rabidaudio/synthesizer/amp/Annotation 2020-08-30 154602.png

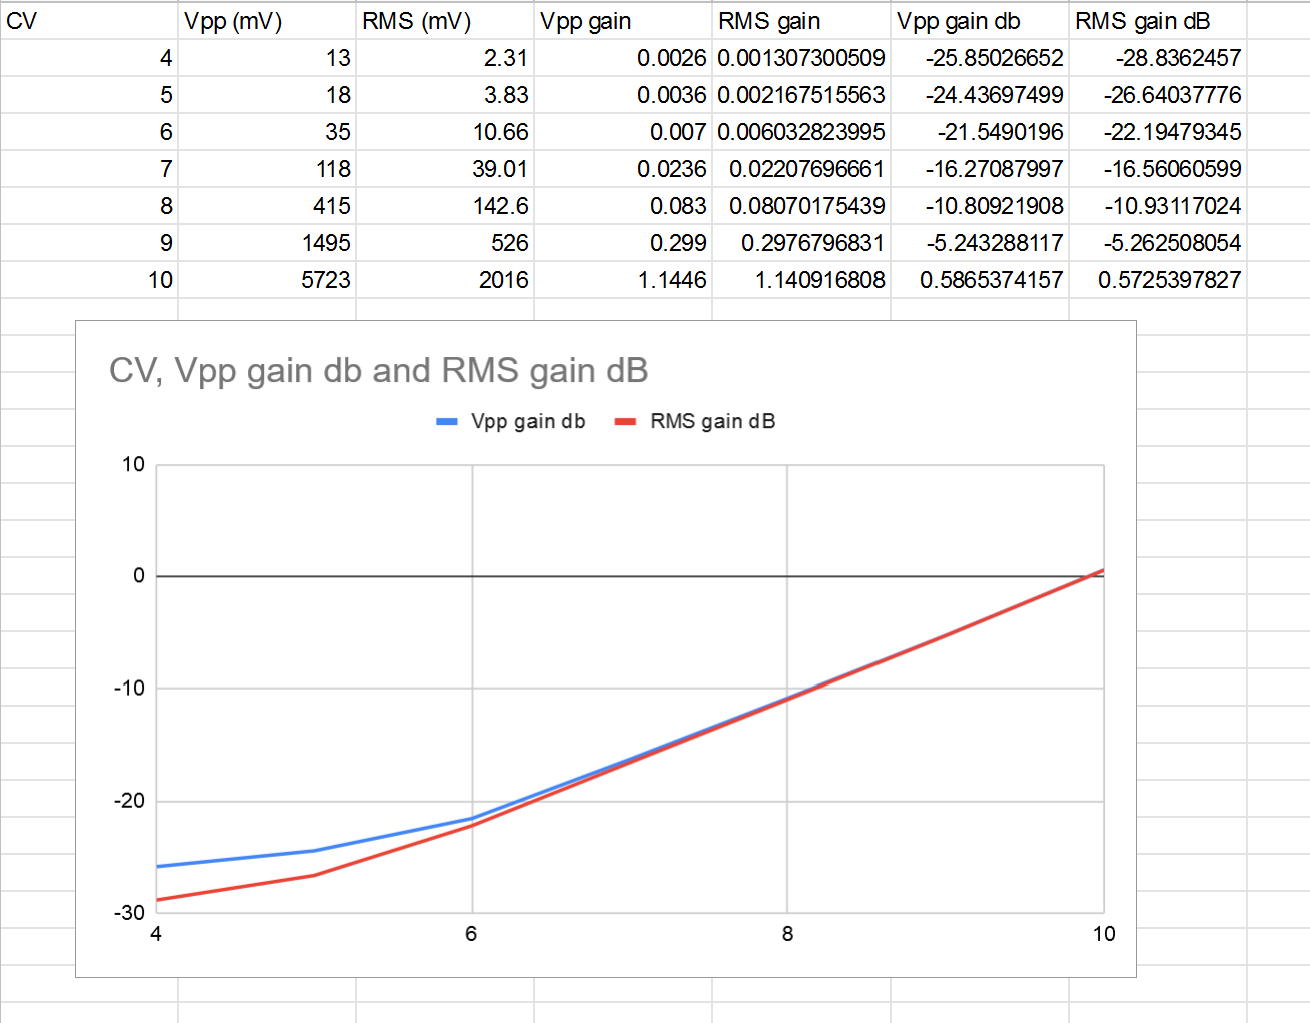
amp/Annotation 2020-08-30 154602.png
