rabidaudio/synthesizer/clock/panel/assets/103_grunge_splatter/Blood-Splatter-006.png

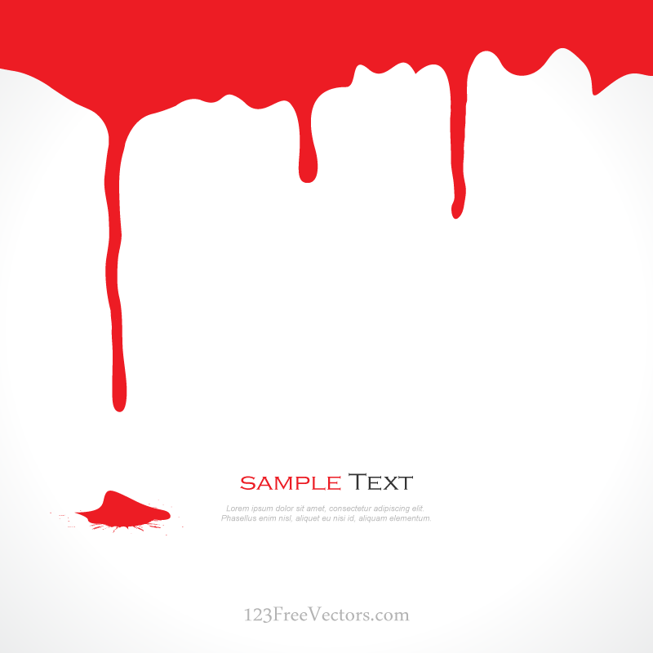
clock/panel/assets/103_grunge_splatter/Blood-Splatter-006.png
