rabidaudio/synthesizer/clock/panel/assets/nosferatu-cine-elhype.jpg

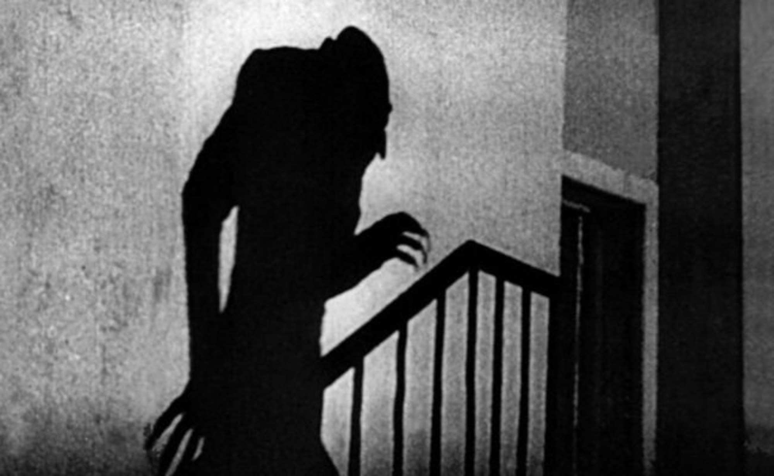
clock/panel/assets/nosferatu-cine-elhype.jpg
