rabidaudio/synthesizer/clock/panel/assets/nosferatu-outline.png

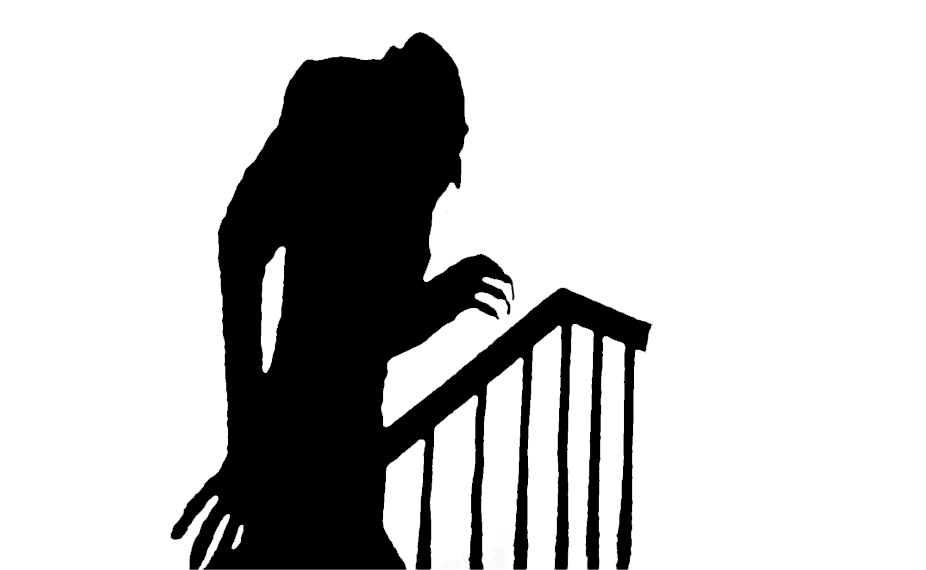
clock/panel/assets/nosferatu-outline.png
