rabidaudio/synthesizer/clock/panel/assets/Schreck.jpg

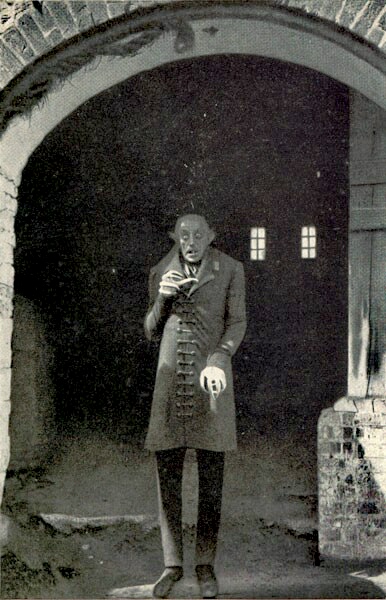
clock/panel/assets/Schreck.jpg
