rabidaudio/synthesizer/vco/vco2.png

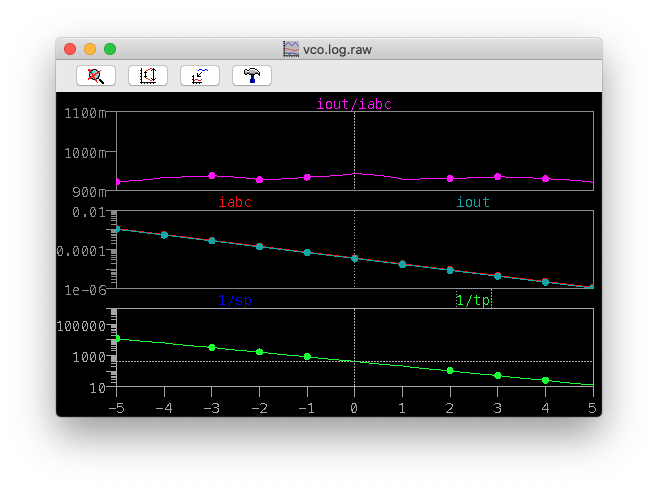
vco/vco2.png
