rabidaudio/synthesizer/vco/waveshaper-plot.png

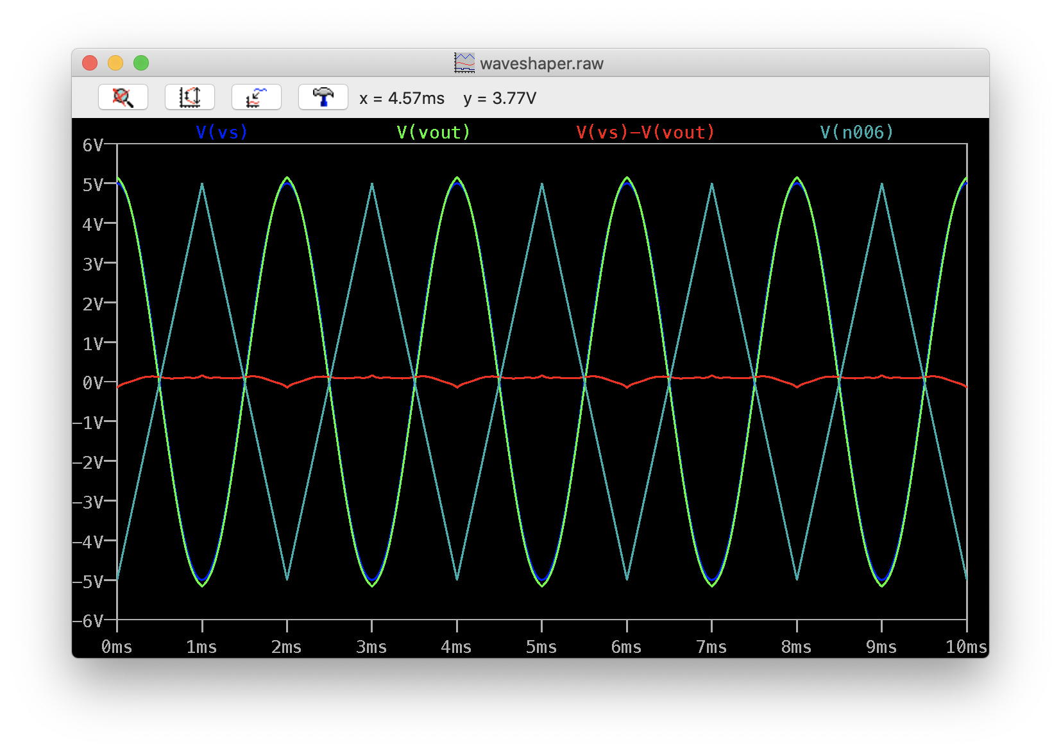
vco/waveshaper-plot.png
