rabidaudio/synthesizer/adsr/Draft1.asc

C1: cap; 4.7µ
I1: current; PULSE(2u -2u 0 0 0 1 2)
R1: res; {RC}
V1: voltage; PULSE(5 -5 0 0 0 1 2)
Named nets: 0, vout
.tran 10 UIC
.step param RC 50k 250k 25K
