rabidaudio/synthesizer/vco/gilbertcell-notworking.asc

Q1: npn
Q2: npn
Q3: npn
Q4: npn
Q5: npn
Q6: npn
R1: res; 3k
R2: res; 6k
R3: res; 6k
R4: res; 6k
U1: tl07x
V1: voltage; 12
V2: voltage; 12
V3: voltage; PULSE(-.1 .1 0 10m 10m 0 20m)
V4: voltage; PULSE(-.1 .1 0 0 0 5m 10m)
Named nets: 0, v+, v-, vo+, vo-, v1, v2
.tran 100m
