rabidaudio/synthesizer/vco/suboctave.asc

A1: dflop
A2: dflop
R1: res; 68K
R2: res; 47K
R3: res; 40k
R4: res; 10k
R5: res; 100k
R6: res; 100k
U1: tl07x
U2: tl07x
U3: ADG1633
U4: tl07x
V1: voltage; 12
V2: voltage; 12
V3: voltage; PULSE(-5 5 0.74m 0 0 0.5m 1m)
V4: voltage; SINE(0 5 1k)
V5: voltage; PULSE(5 0 .5m 0 0 1m 2m)
Named nets: 0, v+, v-, vsin, vsq, ~vsin, vout
.tran 10m
