rabidaudio/synthesizer/vco/vco.asc

C1: cap; 4.7n
Q1: pnp
Q2: pnp
R1: res; 4.7K
R2: res; 1k8
R3: res; 326K
R4: res; 15K
R5: res; 10K
R6: res; 100K
R7: res; 500
R8: res; 500
R9: res; 10K
R10: res; 10K
R11: res; 240K
U1: LM13700
U2: tl07x
U3: tl07x
U4: tl07x
V1: voltage; 12
V2: voltage; 12
V4: voltage; {CV}
Named nets: 0, V-, V+, v+, v-, VCV, sq, tri
.lib lm13700.sub
.lib opamp.sub
## CV-freq analysis ##
#.step param CV 0 10 1
# .tran 0 220m UIC
# .tran 0 8 UIC
# .meas tp TRIG V(tri)=0 RISE=2 TARG V(tri)=0 RISE=3
# .meas sp TRIG V(sq)=0 RISE=2 TARG V(sq)=0 RISE=3
# .meas iabc param -1*Ic(q2)
# .meas TRAN iout param abs(I(C1)) WHEN V(tri)=0 RISE=2
## R6 Analysis CV=5 ##
#.step param RA 98k 102K 100
#.meas tp TRIG V(tri)=0 RISE=2 TARG V(tri)=0 RISE=3
#.param CV 5
#.tran 0 500m UIC
## R3 Analysis CV=0 ##
#.step param RREF 320K 330K 100
#.meas tp TRIG V(tri)=0 RISE=2 TARG V(tri)=0 RISE=3
.tran 10m UIC
## High-freq accuracy CV=-5 ##
# .tran 200u UIC
## DC CV analysis ##
# .dc V4 0 10 1
