rabidaudio/synthesizer/utils/connect-logic.asc

Q1: npn
Q2: npn
R1: res; 100K
R2: res; 100K
R3: res; 100K
R4: res; 100K
V1: voltage; 5
Named nets: 0
.op
