rabidaudio/synthesizer/vco/cv-protection.asc

D1: diode
R1: res; 10k
R2: res; 47k
R3: res; 33k
R4: res; 18k
R5: res; 13k
U1: LT1001
V1: voltage; 12
V2: voltage; 12
V3: voltage; PULSE(-12 12 0 1m 1m 0 2m)
Named nets: 0, V+, V-
.tran 100u 10m
