rabidaudio/synthesizer/clock/src/PauseState.h

#pragma once

#include <Arduino.h>

// Keep track of if output is paused or not
class PauseState
{
private:
    bool _paused = false;
    bool _held = false;
    bool _pressed = false;

public:
    void setState(bool buttonsPressed)
    {
        if (!_held && buttonsPressed)
        {
            _paused = !_paused;
        }
        _held = buttonsPressed;
    }

    // debounce either button to issue tap
    bool isTap(bool buttonPressed)
    {
        if (_pressed == buttonPressed)
        {
            return false;
        }
        _pressed = buttonPressed;
        return buttonPressed;
    }

    bool isPaused()
    {
        return _paused;
    }

    void reset()
    {
        _paused = false;
    }
};
