rabidaudio/synthesizer/clock/src/Timer.h

#pragma once

#include <Arduino.h>
#include <util/atomic.h>
#include "Settings.h"

#define MIN_CLOCK (uint16_t)15
#define MAX_CLOCK (uint16_t)1600
#define MIN_BPM MIN_CLOCK
#define MAX_BPM (MAX_CLOCK / 4)

// Lookup table for OCR1A register values for BPMs from 15 to 1600.
// This is to avoid floating point math.
// 120 BPM = 2 Hz = (16000000/((7811+1)*1024))
// Calculations:
// https://docs.google.com/spreadsheets/d/1pTg9IQDEw8LUGN85Lwp80kAzATN1I9yxx0m5xDrEWBg/edit#gid=0
const PROGMEM uint16_t CLOCK_LOOKUP[] = {
    62500, 58593, 55147, 52083, 49342, 46875, 44642, 42613, 40760, 39062,
    37500, 36057, 34722, 33482, 32327, 31250, 30241, 29296, 28409, 27573,
    26785, 26041, 25337, 24671, 24038, 23437, 22865, 22321, 21802, 21306,
    20833, 20380, 19946, 19531, 19132, 18750, 18382, 18028, 17688, 17361,
    17045, 16741, 16447, 16163, 15889, 15625, 15368, 15120, 14880, 14648,
    14423, 14204, 13992, 13786, 13586, 13392, 13204, 13020, 12842, 12668,
    12500, 12335, 12175, 12019, 11867, 11718, 11574, 11432, 11295, 11160,
    11029, 10901, 10775, 10653, 10533, 10416, 10302, 10190, 10080, 9973,
    9868, 9765, 9664, 9566, 9469, 9375, 9282, 9191, 9101, 9014,
    8928, 8844, 8761, 8680, 8600, 8522, 8445, 8370, 8296, 8223,
    8152, 8081, 8012, 7944, 7878, 7812, 7747, 7684, 7621, 7560,
    7500, 7440, 7381, 7324, 7267, 7211, 7156, 7102, 7048, 6996,
    6944, 6893, 6843, 6793, 6744, 6696, 6648, 6602, 6555, 6510,
    6465, 6421, 6377, 6334, 6291, 6250, 6208, 6167, 6127, 6087,
    6048, 6009, 5971, 5933, 5896, 5859, 5822, 5787, 5751, 5716,
    5681, 5647, 5613, 5580, 5547, 5514, 5482, 5450, 5419, 5387,
    5357, 5326, 5296, 5266, 5237, 5208, 5179, 5151, 5122, 5095,
    5067, 5040, 5013, 4986, 4960, 4934, 4908, 4882, 4857, 4832,
    4807, 4783, 4758, 4734, 4711, 4687, 4664, 4641, 4618, 4595,
    4573, 4550, 4528, 4507, 4485, 4464, 4443, 4422, 4401, 4380,
    4360, 4340, 4320, 4300, 4280, 4261, 4242, 4222, 4204, 4185,
    4166, 4148, 4129, 4111, 4093, 4076, 4058, 4040, 4023, 4006,
    3989, 3972, 3955, 3939, 3922, 3906, 3890, 3873, 3858, 3842,
    3826, 3810, 3795, 3780, 3765, 3750, 3735, 3720, 3705, 3690,
    3676, 3662, 3647, 3633, 3619, 3605, 3591, 3578, 3564, 3551,
    3537, 3524, 3511, 3498, 3485, 3472, 3459, 3446, 3434, 3421,
    3409, 3396, 3384, 3372, 3360, 3348, 3336, 3324, 3312, 3301,
    3289, 3277, 3266, 3255, 3243, 3232, 3221, 3210, 3199, 3188,
    3177, 3167, 3156, 3145, 3135, 3125, 3114, 3104, 3094, 3083,
    3073, 3063, 3053, 3043, 3033, 3024, 3014, 3004, 2995, 2985,
    2976, 2966, 2957, 2948, 2938, 2929, 2920, 2911, 2902, 2893,
    2884, 2875, 2866, 2858, 2849, 2840, 2832, 2823, 2815, 2806,
    2798, 2790, 2781, 2773, 2765, 2757, 2749, 2741, 2733, 2725,
    2717, 2709, 2701, 2693, 2686, 2678, 2670, 2663, 2655, 2648,
    2640, 2633, 2626, 2618, 2611, 2604, 2596, 2589, 2582, 2575,
    2568, 2561, 2554, 2547, 2540, 2533, 2526, 2520, 2513, 2506,
    2500, 2493, 2486, 2480, 2473, 2467, 2460, 2454, 2447, 2441,
    2435, 2428, 2422, 2416, 2410, 2403, 2397, 2391, 2385, 2379,
    2373, 2367, 2361, 2355, 2349, 2343, 2337, 2332, 2326, 2320,
    2314, 2309, 2303, 2297, 2292, 2286, 2281, 2275, 2269, 2264,
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

uint16_t counterValue(uint16_t clock)
{
  return pgm_read_word_near(CLOCK_LOOKUP + clock - MIN_CLOCK);
}

// Core clock source. Async using Timer1.
// Will toggle provided pins at the requested BPM.
// Timer1 is a 16-bit two comparison timer, configured with a pre-scaler of 1024
// on the 16MHz clock speed. That means the counter ticks every 64us.
// When the counter reaches OCR1A the counter resets to zero and the pins
// are brought high. When the counter reaches OCR1B (~12ms), the pins are
// brought low.
// To support the subdivision function, the timer clock is set to the frequency
// of either beat or subdiv, whichever is higher. The other then is an integer
// subdivision, counting down _subdivIdx on each of the higher frequency's beats.
// For the swing function, two different timer values are calculated, one ahead
// and one behind. The timer switches OCR1A between the two clock values on each
// beat.
// TO support the swing function, _swingOffset is calculated as a drift forward
// or backward from the base clock value. It's up to a third early or late. On
// each tick, the clock is adjusted by this amount forwards (on even ticks) or
// backward (on odd ticks).
class Timer1
{
private:
  uint16_t _baseBPM;
  uint16_t _bpmOffset = 0;
  uint8_t _beatPin;
  uint8_t _subdivPin;
  int8_t _subdivisions;
  int8_t _swing;
  bool _enabled = false;
  volatile uint8_t _subdivIdx;
  volatile uint16_t _clock;
  volatile int16_t _swingOffset = 0;
  volatile bool _isEven = true;
  volatile bool _clockHigh = false;
  volatile bool _subdivHigh = false;

  void updateTimer()
  {
    uint16_t clock = counterValue(getClock());
    // Note: Hopefully doing this math isn't too slow.
    // It only needs to happen when the swing or bpm changes.
    // Convert a percentage value into a scale value, where
    // 0% => straight, 66% => triplets, 50% => quarters, etc.
    // Here, we want 66% to actually be 66.666%, so rather than
    // 200, we use 66*3 = 198.
    float swingScale = ((float)_swing) / 198.0;
    float offsetF = ((float)clock) * swingScale;
    int16_t offset = (int16_t)offsetF;
    ATOMIC_BLOCK(ATOMIC_RESTORESTATE)
    {
      _clock = clock;
      _swingOffset = offset;
    }
  }

  // returns true if subdiv is an integer multiple of beat.
  // returns false if subdiv is a subdivision and therefore
  // beat is actually an integer multiple of it
  inline bool isSuperdivisionMode()
  {
    return _subdivisions < 0;
  }

  inline size_t highFreqPin()
  {
    return isSuperdivisionMode() ? _beatPin : _subdivPin;
  }

  inline size_t lowFreqPin()
  {
    return isSuperdivisionMode() ? _subdivPin : _beatPin;
  }

public:
  void begin(uint8_t beatPin, uint8_t subdivPin, Settings settings)
  {
    _beatPin = beatPin;
    _subdivPin = subdivPin;
    pinMode(_beatPin, OUTPUT);
    pinMode(_subdivPin, OUTPUT);
    loadSettings(settings);
    reset();

    noInterrupts();
    // Clear registers
    TCCR1A = 0;
    TCCR1B = 0;
    TCNT1 = 0;

    OCR1A = 1000;
    // TODO: allow pulse width to be customized, or at least
    // dynamic to frequency
    OCR1B = 250; // 16ms, approx 50% pulse width at max frequency

    // TCCR1B |= (1 << WGM12); // CTC
    //  Phase and frequency correct PWM
    TCCR1A |= (0 << WGM11) | (1 << WGM10);
    TCCR1B |= (1 << WGM13) | (0 << WGM12);

    // Pre-scaler 1024
    TCCR1B |= (1 << CS12) | (0 << CS11) | (1 << CS10);

    updateTimer();
    setEnabled(true);
    interrupts();
  }

  void setEnabled(bool enabled)
  {
    if (_enabled == enabled)
    {
      return;
    }
    if (enabled)
    {
      // Output Compare Match A Interrupt Enable
      TIMSK1 |= (1 << OCIE1A) | (1 << OCIE1B);
    }
    else
    {
      TIMSK1 &= ~((1 << OCIE1A) | (1 << OCIE1B));
    }
    _enabled = enabled;
  }

  void setSwing(int8_t swing)
  {
    if (swing != _swing)
    {
      _swing = constrain(swing, -75, 75);
      updateTimer();
    }
  }

  int8_t getSwing()
  {
    return _swing;
  }

  int16_t incrementSwing(int8_t swing)
  {
    setSwing(_swing + swing);
    return _swing;
  }

  void setBaseBPM(uint16_t bpm)
  {
    if (bpm != _baseBPM)
    {
      _baseBPM = constrain(bpm, MIN_BPM, MAX_BPM);
      updateTimer();
    }
  }

  uint16_t getBaseBPM()
  {
    return _baseBPM;
  }

  uint16_t incrementBaseBPM(int16_t amount)
  {
    if (amount != 0)
    {
      setBaseBPM(_baseBPM + amount);
    }
    return _baseBPM;
  }

  void setBPMOffset(uint16_t offset)
  {
    if (offset != _bpmOffset)
    {
      _bpmOffset = offset;
      updateTimer();
    }
  }

  uint16_t getBPM()
  {
    return constrain(_baseBPM + _bpmOffset, MIN_BPM, MAX_BPM);
  }

  uint16_t getClock()
  {
    uint16_t clock = getBPM();
    if (_subdivisions > 1)
    {
      clock = clock * _subdivisions;
    }
    return constrain(clock, MIN_CLOCK, MAX_CLOCK);
  }

  uint8_t incrementSubdivisions(int8_t amount)
  {
    if (amount == 0)
    {
      return _subdivisions;
    }
    while (amount != 0)
    {
      if (amount > 0)
      {
        _subdivisions++;
        if (_subdivisions > 4)
          _subdivisions = 4;
        if (_subdivisions == -1 || _subdivisions == 0)
          _subdivisions = 1;
        amount--;
      }
      else
      {
        _subdivisions--;
        if (_subdivisions < -8)
          _subdivisions = -8;
        if (_subdivisions == -1 || _subdivisions == 0)
          _subdivisions = -2;
        amount++;
      }
    }
    updateTimer();
    return _subdivisions;
  }

  // Allowed values: {-4, -3, -2, 1, 2, 3, 4, 5, 6, 7, 8}
  // N < 0 -> one subdiv tick every N beats
  // N >= 1 -> N subdiv ticks per beat
  void setSubdivisions(int8_t subdiv)
  {
    _subdivisions = constrain(subdiv, -4, 8);
    if (subdiv == -1 || subdiv == 0)
    {
      _subdivisions = 1;
    }
  }

  uint8_t getSubdivisions()
  {
    return _subdivisions;
  }

  void reset()
  {
    ATOMIC_BLOCK(ATOMIC_RESTORESTATE)
    {
      _subdivIdx = 1; // cause subdiv to tick on next
      _isEven = true;
      OCR1A = _clock - _swingOffset;
      TCNT1 = 0; // reset timer
    }
  }

  void loadSettings(Settings settings)
  {
    setSubdivisions(settings.subdivisions);
    setBaseBPM(settings.baseBPM);
    setSwing(settings.swing);
  }

  Settings getCurrentSettings()
  {
    Settings s;
    s.baseBPM = _baseBPM;
    s.subdivisions = _subdivisions;
    s.swing = _swing;
    return s;
  }

  // trigger a single step of the beat. Blocking.
  // useful for stepping a sequencer back to the beginning.
  void singleTick()
  {
    tickA();
    delay(12);
    tickB();
  }

  bool beatOn()
  {
    return isSuperdivisionMode() ? _clockHigh : _subdivHigh;
  }

  bool subdivOn()
  {
    return isSuperdivisionMode() ? _subdivHigh : _clockHigh;
  }

  inline void tickA()
  {

    TCNT1 = 0; // reset timer

    // If the clock has changed tempo has changed, update it
    OCR1A = _isEven ? (_clock - _swingOffset) : (_clock + _swingOffset);
    _isEven = !_isEven;
    // This is not required using phase+frequency correct mode
    // as OCR1A is buffered
    // if (TCNT1 > OCR1A)
    //   TCNT1 = 0; // reset timer
    digitalWrite(highFreqPin(), HIGH);
    _clockHigh = true;
    _subdivIdx--;
    if (_subdivIdx == 0)
    {
      digitalWrite(lowFreqPin(), HIGH);
      _subdivHigh = true;
      // restart subdivisions
      _subdivIdx = abs(_subdivisions);
    }
  }

  inline void tickB()
  {
    digitalWrite(_beatPin, LOW);
    digitalWrite(_subdivPin, LOW);
    _clockHigh = false;
    _subdivHigh = false;
  }
};

// Global instance, since only one Timer1 exists
Timer1 Timer;

ISR(TIMER1_COMPA_vect)
{
  Timer.tickA();
}

ISR(TIMER1_COMPB_vect)
{
  Timer.tickB();
}
